shorepine/amychip/Arduino/pcm9211/wm8960.c

// wm89602.c

/******************************************************************************
  SparkFun WM8960 Arduino Library

  This library provides a set of functions to control (via I2C) the Wolfson 
  Microelectronics WM8960   Stereo CODEC with 1W Stereo Class D Speaker Drivers 
  and Headphone Drivers.

  Pete Lewis @ SparkFun Electronics
  October 14th, 2022
  https://github.com/sparkfun/SparkFun_WM8960_Arduino_Library
  
  This code was created using some code by Mike Grusin at SparkFun Electronics
  Included with the LilyPad MP3 example code found here:
  Revision history: version 1.0 2012/07/24 MDG Initial release
  https://github.com/sparkfun/LilyPad_MP3_Player

  Do you like this library? Help support SparkFun. Buy a board!

    SparkFun Audio Codec Breakout - WM8960 (QWIIC)
    https://www.sparkfun.com/products/21250
    
    All functions return 1 if the read/write was successful, and 0
    if there was a communications failure. You can ignore the return value
    if you just don't care anymore.

    For information on the data sent to and received from the CODEC,
    refer to the WM8960 datasheet at:
    https://github.com/sparkfun/SparkFun_Audio_Codec_Breakout_WM8960/blob/main/Documents/WM8960_datasheet_v4.2.pdf

  This code is released under the [MIT License](http://opensource.org/licenses/MIT).
  Please review the LICENSE.md file included with this example. If you have any questions 
  or concerns with licensing, please contact techsupport@sparkfun.com.
  Distributed as-is; no warranty is given.
******************************************************************************/

#include "wm8960.h"

// The WM8960 does not support I2C reads
// This means we must keep a local copy of all the register values
// We will instantiate with default values
// As we write to the device, we will also make sure
// To update our local copy as well, stored here in this array.
// Each register is 9-bits, so we will store them as a uint16_t
// They are in order from R0-R55, and we even keep blank spots for the
// "reserved" registers. This way we can use the register address macro 
// defines above to easiy access each local copy of each register.
// Example: _registerLocalCopy[WM8960_REG_LEFT_INPUT_VOLUME]
uint16_t _registerLocalCopy[56] = {
    0x0097, // R0 (0x00)
    0x0097, // R1 (0x01)
    0x0000, // R2 (0x02)
    0x0000, // R3 (0x03)
    0x0000, // R4 (0x04)
    0x0008, // F5 (0x05)
    0x0000, // R6 (0x06)
    0x000A, // R7 (0x07)
    0x01C0, // R8 (0x08)
    0x0000, // R9 (0x09)
    0x00FF, // R10 (0x0a)
    0x00FF, // R11 (0x0b)
    0x0000, // R12 (0x0C) RESERVED
    0x0000, // R13 (0x0D) RESERVED
    0x0000, // R14 (0x0E) RESERVED
    0x0000, // R15 (0x0F) RESERVED
    0x0000, // R16 (0x10)
    0x007B, // R17 (0x11)
    0x0100, // R18 (0x12)
    0x0032, // R19 (0x13)
    0x0000, // R20 (0x14)
    0x00C3, // R21 (0x15)
    0x00C3, // R22 (0x16)
    0x01C0, // R23 (0x17)
    0x0000, // R24 (0x18)
    0x0000, // R25 (0x19)
    0x0000, // R26 (0x1A)
    0x0000, // R27 (0x1B)
    0x0000, // R28 (0x1C)
    0x0000, // R29 (0x1D)
    0x0000, // R30 (0x1E) RESERVED
    0x0000, // R31 (0x1F) RESERVED
    0x0100, // R32 (0x20)
    0x0100, // R33 (0x21)
    0x0050, // R34 (0x22)
    0x0000, // R35 (0x23) RESERVED
    0x0000, // R36 (0x24) RESERVED
    0x0050, // R37 (0x25)
    0x0000, // R38 (0x26)
    0x0000, // R39 (0x27)
    0x0000, // R40 (0x28)
    0x0000, // R41 (0x29)
    0x0040, // R42 (0x2A)
    0x0000, // R43 (0x2B)
    0x0000, // R44 (0x2C)
    0x0050, // R45 (0x2D)
    0x0050, // R46 (0x2E)
    0x0000, // R47 (0x2F)
    0x0002, // R48 (0x30)
    0x0037, // R49 (0x31)
    0x0000, // R50 (0x32) RESERVED
    0x0080, // R51 (0x33)
    0x0008, // R52 (0x34)
    0x0031, // R53 (0x35)
    0x0026, // R54 (0x36)
    0x00e9, // R55 (0x37)
};

const uint16_t _registerDefaults[56] = {
    0x0097, // R0 (0x00)
    0x0097, // R1 (0x01)
    0x0000, // R2 (0x02)
    0x0000, // R3 (0x03)
    0x0000, // R4 (0x04)
    0x0008, // F5 (0x05)
    0x0000, // R6 (0x06)
    0x000A, // R7 (0x07)
    0x01C0, // R8 (0x08)
    0x0000, // R9 (0x09)
    0x00FF, // R10 (0x0a)
    0x00FF, // R11 (0x0b)
    0x0000, // R12 (0x0C) RESERVED
    0x0000, // R13 (0x0D) RESERVED
    0x0000, // R14 (0x0E) RESERVED
    0x0000, // R15 (0x0F) RESERVED
    0x0000, // R16 (0x10)
    0x007B, // R17 (0x11)
    0x0100, // R18 (0x12)
    0x0032, // R19 (0x13)
    0x0000, // R20 (0x14)
    0x00C3, // R21 (0x15)
    0x00C3, // R22 (0x16)
    0x01C0, // R23 (0x17)
    0x0000, // R24 (0x18)
    0x0000, // R25 (0x19)
    0x0000, // R26 (0x1A)
    0x0000, // R27 (0x1B)
    0x0000, // R28 (0x1C)
    0x0000, // R29 (0x1D)
    0x0000, // R30 (0x1E) RESERVED
    0x0000, // R31 (0x1F) RESERVED
    0x0100, // R32 (0x20)
    0x0100, // R33 (0x21)
    0x0050, // R34 (0x22)
    0x0000, // R35 (0x23) RESERVED
    0x0000, // R36 (0x24) RESERVED
    0x0050, // R37 (0x25)
    0x0000, // R38 (0x26)
    0x0000, // R39 (0x27)
    0x0000, // R40 (0x28)
    0x0000, // R41 (0x29)
    0x0040, // R42 (0x2A)
    0x0000, // R43 (0x2B)
    0x0000, // R44 (0x2C)
    0x0050, // R45 (0x2D)
    0x0050, // R46 (0x2E)
    0x0000, // R47 (0x2F)
    0x0002, // R48 (0x30)
    0x0037, // R49 (0x31)
    0x0000, // R50 (0x32) RESERVED
    0x0080, // R51 (0x33)
    0x0008, // R52 (0x34)
    0x0031, // R53 (0x35)
    0x0026, // R54 (0x36)
    0x00e9, // R55 (0x37)
};   


// This sets up with OUT3/HP at line level volume
// and with INPUT1 ADC coming in to i2s
void setup_wm8960_i2s() {

    enableVREF();
    enableVMID();

    enableLMIC();
    enableRMIC();

    connectLMN1();
    connectRMN1();

    disableLINMUTE();
    disableRINMUTE();
    
    setLINVOLDB(0);
    setRINVOLDB(0);
    
    setLMICBOOST(WM8960_MIC_BOOST_GAIN_0DB);
    setRMICBOOST(WM8960_MIC_BOOST_GAIN_0DB);

    connectLMIC2B();
    connectRMIC2B();

    enableAINL();
    enableAINR();
    
    disableLB2LO();
    disableRB2RO();

    enableLD2LO();
    enableRD2RO();
    setLB2LOVOL(WM8960_OUTPUT_MIXER_GAIN_NEG_21DB); 
    setRB2ROVOL(WM8960_OUTPUT_MIXER_GAIN_NEG_21DB); 

    enableLOMIX();
    enableROMIX();

    enablePLL();
    setPLLPRESCALE(WM8960_PLLPRESCALE_DIV_2);
    setSMD(WM8960_PLL_MODE_FRACTIONAL);
    setCLKSEL(WM8960_CLKSEL_PLL);
    setSYSCLKDIV(WM8960_SYSCLK_DIV_BY_2);
    setBCLKDIV(4);
    setDCLKDIV(WM8960_DCLKDIV_16);
    setPLLN(7);
    setPLLK(0x86, 0xC2, 0x26);
    setWL(WM8960_WL_16BIT);
    enablePeripheralMode();

    enableAdcLeft();
    enableAdcRight();

    enableDacLeft();
    enableDacRight();
    disableDacMute();

    disableLoopBack();

    disableDacMute();

    enableHeadphones();
    enableOUT3MIX();
    setHeadphoneVolumeDB(0.00); // line level 
}


extern void i2c_master_write_wm8960(uint8_t *data_wr, size_t size_wr);

// writeRegister(uint8_t reg, uint16_t value)
// General-purpose write to a register
// Returns 1 if successful, 0 if something failed (I2C error)
// The WM8960 has 9 bit registers.
// To write a register, we must do the following
// Send 3 bytes
// Byte0 = device address + read/write bit
// Control_byte_1 = register-to-write address (7-bits) plus 9th bit of data
// Control_byte_2 = remaining 8 bits of register data

void writeRegister(uint8_t reg, uint16_t value) {
  uint8_t data[2];

  // Shift reg over one spot to make room for the 9th bit of register data
  data[0] = (reg << 1); 
  
  // Shift value so only 9th bit is still there, plug it into 0th bit of 
  // control_byte_1
  data[0] |= (value >> 8); 

  data[1] = (uint8_t)(value & 0xFF);
  i2c_master_write_wm8960(data,2);  
}

// writeRegisterBit
// Writes a 0 or 1 to the desired bit in the desired register
void _writeRegisterBit(uint8_t registerAddress, uint8_t bitNumber, uint8_t bitValue)
{
    // Get the local copy of the register
    uint16_t regvalue = _registerLocalCopy[registerAddress]; 

    if(bitValue == 1) 
    {
      regvalue |= (1<<bitNumber); // Set only the bit we want  
    }
    else {
      regvalue &= ~(1<<bitNumber); // Clear only the bit we want  
    }

    // Write modified value to device
    // If successful, update local copy
    writeRegister(registerAddress, regvalue);
    _registerLocalCopy[registerAddress] = regvalue; 
}

// writeRegisterMultiBits
// This function writes data into the desired bits within the desired register
// Some settings require more than just flipping a single bit within a register.
// For these settings use this more advanced register write helper function.
// 
// For example, to change the LIN2BOOST setting to +6dB,
// I need to write a setting of 7 (aka +6dB) to the bits [3:1] in the 
// WM8960_REG_INPUT_BOOST_MIXER_1 register. Like so...
// _writeRegisterMultiBits(WM8960_REG_INPUT_BOOST_MIXER_1, 3, 1, 7);
void _writeRegisterMultiBits(uint8_t registerAddress, uint8_t settingMsbNum, uint8_t settingLsbNum, uint8_t setting)
{
  uint8_t numOfBits = (settingMsbNum - settingLsbNum) + 1;

  // Get the local copy of the register
  uint16_t regvalue = _registerLocalCopy[registerAddress]; 

  for(int i = 0 ; i < numOfBits ; i++)
  {
      regvalue &= ~(1 << (settingLsbNum + i)); // Clear bits we care about 
  }

  // Shift and set the bits from in incoming desired setting value
  regvalue |= (setting << settingLsbNum); 

  // Write modified value to device
  // If successful, update local copy
  writeRegister(registerAddress, regvalue);
  _registerLocalCopy[registerAddress] = regvalue; 
}

// enableVREF
// Necessary for all other functions of the CODEC
// VREF is a single bit we can flip in Register 25 (19h), WM8960_REG_PWR_MGMT_1
// VREF is bit 6, 0 = power down, 1 = power up
// Returns 1 if successful, 0 if something failed (I2C error)
void enableVREF()
{ 
  _writeRegisterBit(WM8960_REG_PWR_MGMT_1, 6, 1);
}

// disableVREF
// Use this to save power
// VREF is a single bit we can flip in Register 25 (19h), WM8960_REG_PWR_MGMT_1
// VREF is bit 6, 0 = power down, 1 = power up
// Returns 1 if successful, 0 if something failed (I2C error)
void disableVREF()
{
  _writeRegisterBit(WM8960_REG_PWR_MGMT_1, 6, 0);
}

// reset
// Use this to reset all registers to their default state
// Note, this can also be done by cycling power to the device
// Returns 1 if successful, 0 if something failed (I2C error)
void reset()
{
  // Doesn't matter which bit we flip, writing anything will cause the reset
  _writeRegisterBit(WM8960_REG_RESET, 7, 1);
  // Update our local copy of the registers to reflect the reset
  for(int i = 0 ; i < 56 ; i++)
  {
    _registerLocalCopy[i] = _registerDefaults[i]; 
  }
}

void enableAINL()
{ 
  _writeRegisterBit(WM8960_REG_PWR_MGMT_1, 5, 1);
}

void disableAINL()
{ 
  _writeRegisterBit(WM8960_REG_PWR_MGMT_1, 5, 0);
}

void enableAINR()
{
  _writeRegisterBit(WM8960_REG_PWR_MGMT_1, 4, 1);
}

void disableAINR()
{
  _writeRegisterBit(WM8960_REG_PWR_MGMT_1, 4, 0);
}

void enableLMIC()
{
  _writeRegisterBit(WM8960_REG_PWR_MGMT_3, 5, 1);
}

void disableLMIC()
{
  _writeRegisterBit(WM8960_REG_PWR_MGMT_3, 5, 0);
}

void enableRMIC()
{
  _writeRegisterBit(WM8960_REG_PWR_MGMT_3, 4, 1);
}

void disableRMIC()
{
  _writeRegisterBit(WM8960_REG_PWR_MGMT_3, 4, 0);
}

void enableLMICBOOST()
{
  _writeRegisterBit(WM8960_REG_PWR_MGMT_3, 5, 1);
}

void disableLMICBOOST()
{
  _writeRegisterBit(WM8960_REG_PWR_MGMT_3, 5, 0);
}

void enableRMICBOOST()
{
  _writeRegisterBit(WM8960_REG_PWR_MGMT_3, 4, 1);
}

void disableRMICBOOST()
{
  _writeRegisterBit(WM8960_REG_PWR_MGMT_3, 4, 0);
}

// PGA input signal select
// Each PGA (left and right) has a switch on its non-inverting input.
// On PGA_LEFT:
//  *You can select between VMID, LINPUT2 or LINPUT3
//  *Note, the inverting input of PGA_LEFT is perminantly connected to LINPUT1
// On PGA_RIGHT:
//  *You can select between VMIN, RINPUT2 or RINPUT3
//  *Note, the inverting input of PGA_RIGHT is perminantly connected to RINPUT1

// 3 options: WM8960_PGAL_LINPUT2, WM8960_PGAL_LINPUT3, WM8960_PGAL_VMID
void pgaLeftNonInvSignalSelect(uint8_t signal)
{
  // Clear LMP2 and LMP3
  // Necessary because the previous setting could have either set,
  // And we don't want to confuse the codec.
  // Only 1 input can be selected.

  // LMP3
  _writeRegisterBit(WM8960_REG_ADCL_SIGNAL_PATH, 7, 0); 

  // LMP2
  _writeRegisterBit(WM8960_REG_ADCL_SIGNAL_PATH, 6, 0); 
  
  if(signal == WM8960_PGAL_LINPUT2)
  {
    // LMP2
    _writeRegisterBit(WM8960_REG_ADCL_SIGNAL_PATH, 6, 1); 
  }
  else if(signal == WM8960_PGAL_LINPUT3)
  {
    // LMP3
    _writeRegisterBit(WM8960_REG_ADCL_SIGNAL_PATH, 7, 1); 
  }
  else if(signal == WM8960_PGAL_VMID)
  {
    // Don't set any bits. When both LMP2 and LMP3 are cleared, then the signal 
    // is set to VMID
  }
}

 // 3 options: WM8960_PGAR_RINPUT2, WM8960_PGAR_RINPUT3, WM8960_PGAR_VMID
void pgaRightNonInvSignalSelect(uint8_t signal)
{
  // Clear RMP2 and RMP3
  // Necessary because the previous setting could have either set,
  // And we don't want to confuse the codec.
  // Only 1 input can be selected.

  // RMP3
  _writeRegisterBit(WM8960_REG_ADCR_SIGNAL_PATH, 7, 0); 

  // RMP2
  _writeRegisterBit(WM8960_REG_ADCR_SIGNAL_PATH, 6, 0); 
  
  if(signal == WM8960_PGAR_RINPUT2)
  {
    // RMP2
    _writeRegisterBit(WM8960_REG_ADCR_SIGNAL_PATH, 6, 1); 
  }
  else if(signal == WM8960_PGAR_RINPUT3)
  {
    // RMP3
    _writeRegisterBit(WM8960_REG_ADCR_SIGNAL_PATH, 7, 1); 
  }
  else if(signal == WM8960_PGAR_VMID)
  {
    // Don't set any bits. When both RMP2 and RMP3 are cleared, then the signal 
    // is set to VMID
  }
}


// Connection from each INPUT1 to the inverting input of its PGA
void connectLMN1()
{
  _writeRegisterBit(WM8960_REG_ADCL_SIGNAL_PATH, 8, 1);
}

// Disconnect LINPUT1 to inverting input of Left Input PGA
void disconnectLMN1()
{
  _writeRegisterBit(WM8960_REG_ADCL_SIGNAL_PATH, 8, 0);
}

// Connect RINPUT1 from inverting input of Right Input PGA
void connectRMN1()
{
  _writeRegisterBit(WM8960_REG_ADCR_SIGNAL_PATH, 8, 1);
}

// Disconnect RINPUT1 to inverting input of Right Input PGA
void disconnectRMN1()
{
  _writeRegisterBit(WM8960_REG_ADCR_SIGNAL_PATH, 8, 0);
}

// Connections from output of PGAs to downstream "boost mixers".

// Connect Left Input PGA to Left Input Boost mixer
void connectLMIC2B()
{
  _writeRegisterBit(WM8960_REG_ADCL_SIGNAL_PATH, 3, 1);
}

// Disconnect Left Input PGA to Left Input Boost mixer
void disconnectLMIC2B()
{
  _writeRegisterBit(WM8960_REG_ADCL_SIGNAL_PATH, 3, 0);
}

// Connect Right Input PGA to Right Input Boost mixer
void connectRMIC2B()
{
  _writeRegisterBit(WM8960_REG_ADCR_SIGNAL_PATH, 3, 1);
}

// Disconnect Right Input PGA to Right Input Boost mixer
void disconnectRMIC2B()
{
  _writeRegisterBit(WM8960_REG_ADCR_SIGNAL_PATH, 3, 0);
}

// 0-63, (0 = -17.25dB) <<-- 0.75dB steps -->> (63 = +30dB)
void setLINVOL(uint8_t volume) 
{
  if(volume > 63) volume = 63; // Limit incoming values max
  _writeRegisterMultiBits(WM8960_REG_LEFT_INPUT_VOLUME,5,0,volume);
  pgaLeftIPVUSet();
}

// setLINVOLDB
// Sets the volume of the PGA input buffer amp to a specified dB value 
// passed in as a float argument.
// Valid dB settings are -17.25 up to +30.00
// -17.25 = -17.25dB (MIN)
// ... 0.75dB steps ...
// 30.00 = +30.00dB  (MAX)
void setLINVOLDB(float dB)
{
  // Create an unsigned integer volume setting variable we can send to 
  // setLINVOL()
  uint8_t volume = convertDBtoSetting(dB, WM8960_PGA_GAIN_OFFSET, WM8960_PGA_GAIN_STEPSIZE, WM8960_PGA_GAIN_MIN, WM8960_PGA_GAIN_MAX);

  setLINVOL(volume);
}

// 0-63, (0 = -17.25dB) <<-- 0.75dB steps -->> (63 = +30dB)
void setRINVOL(uint8_t volume) 
{
  if(volume > 63) volume = 63; // Limit incoming values max
  _writeRegisterMultiBits(WM8960_REG_RIGHT_INPUT_VOLUME,5,0,volume);
  pgaRightIPVUSet();
}

// setRINVOLDB
// Sets the volume of the PGA input buffer amp to a specified dB value 
// passed in as a float argument.
// Valid dB settings are -17.25 up to +30.00
// -17.25 = -17.25dB (MIN)
// ... 0.75dB steps ...
// 30.00 = +30.00dB  (MAX)
void setRINVOLDB(float dB)
{
  // Create an unsigned integer volume setting variable we can send to 
  // setRINVOL()
  uint8_t volume = convertDBtoSetting(dB, WM8960_PGA_GAIN_OFFSET, WM8960_PGA_GAIN_STEPSIZE, WM8960_PGA_GAIN_MIN, WM8960_PGA_GAIN_MAX);
  setRINVOL(volume);
}

// Zero Cross prevents zipper sounds on volume changes
// Sets both left and right PGAs
void enablePgaZeroCross()
{
  _writeRegisterBit(WM8960_REG_LEFT_INPUT_VOLUME, 6, 1);
  _writeRegisterBit(WM8960_REG_RIGHT_INPUT_VOLUME, 6, 1);
}

void disablePgaZeroCross()
{
  _writeRegisterBit(WM8960_REG_LEFT_INPUT_VOLUME, 6, 0);
  _writeRegisterBit(WM8960_REG_RIGHT_INPUT_VOLUME, 6, 0);
}

void enableLINMUTE()
{
  _writeRegisterBit(WM8960_REG_LEFT_INPUT_VOLUME, 7, 1);
}

void disableLINMUTE()
{
  _writeRegisterBit(WM8960_REG_LEFT_INPUT_VOLUME, 7, 0);
  _writeRegisterBit(WM8960_REG_LEFT_INPUT_VOLUME, 8, 1);
}

void enableRINMUTE()
{
  _writeRegisterBit(WM8960_REG_RIGHT_INPUT_VOLUME, 7, 1);
}

void disableRINMUTE()
{
  _writeRegisterBit(WM8960_REG_RIGHT_INPUT_VOLUME, 7, 0);
  _writeRegisterBit(WM8960_REG_RIGHT_INPUT_VOLUME, 8, 1);
}

// Causes left and right input PGA volumes to be updated (LINVOL and RINVOL)
void pgaLeftIPVUSet()
{
  _writeRegisterBit(WM8960_REG_LEFT_INPUT_VOLUME, 8, 1);
}

 // Causes left and right input PGA volumes to be updated (LINVOL and RINVOL)
void pgaRightIPVUSet()
{
  _writeRegisterBit(WM8960_REG_RIGHT_INPUT_VOLUME, 8, 1);
}


// Input Boosts

// 0-3, 0 = +0dB, 1 = +13dB, 2 = +20dB, 3 = +29dB
void setLMICBOOST(uint8_t boost_gain) 
{
  if(boost_gain > 3) boost_gain = 3; // Limit incoming values max
  _writeRegisterMultiBits(WM8960_REG_ADCL_SIGNAL_PATH,5,4,boost_gain);
}

// 0-3, 0 = +0dB, 1 = +13dB, 2 = +20dB, 3 = +29dB
void setRMICBOOST(uint8_t boost_gain) 
{
  if(boost_gain > 3) boost_gain = 3; // Limit incoming values max
  _writeRegisterMultiBits(WM8960_REG_ADCR_SIGNAL_PATH,5,4,boost_gain);
}

// 0-7, 0 = Mute, 1 = -12dB ... 3dB steps ... 7 = +6dB
void setLIN3BOOST(uint8_t boost_gain) 
{
  if(boost_gain > 7) boost_gain = 7; // Limit incoming values max
  _writeRegisterMultiBits(WM8960_REG_INPUT_BOOST_MIXER_1,6,4,boost_gain);
}

// 0-7, 0 = Mute, 1 = -12dB ... 3dB steps ... 7 = +6dB
void setLIN2BOOST(uint8_t boost_gain) 
{
  if(boost_gain > 7) boost_gain = 7; // Limit incoming values max
  _writeRegisterMultiBits(WM8960_REG_INPUT_BOOST_MIXER_1,3,1,boost_gain);
}

// 0-7, 0 = Mute, 1 = -12dB ... 3dB steps ... 7 = +6dB
void setRIN3BOOST(uint8_t boost_gain) 
{
  if(boost_gain > 7) boost_gain = 7; // Limit incoming values max
  _writeRegisterMultiBits(WM8960_REG_INPUT_BOOST_MIXER_2,6,4,boost_gain);
}

// 0-7, 0 = Mute, 1 = -12dB ... 3dB steps ... 7 = +6dB  
void setRIN2BOOST(uint8_t boost_gain) 
{
  if(boost_gain > 7) boost_gain = 7; // Limit incoming values max
  _writeRegisterMultiBits(WM8960_REG_INPUT_BOOST_MIXER_2,3,1,boost_gain);
}

// Mic Bias control
void enableMicBias()
{
  _writeRegisterBit(WM8960_REG_PWR_MGMT_1, 1, 1);
}

void disableMicBias()
{
  _writeRegisterBit(WM8960_REG_PWR_MGMT_1, 1, 0);
}

// WM8960_MIC_BIAS_VOLTAGE_0_9_AVDD (0.9*AVDD) 
// or WM8960_MIC_BIAS_VOLTAGE_0_65_AVDD (0.65*AVDD)
void setMicBiasVoltage(uint8_t voltage)
{
  _writeRegisterBit(WM8960_REG_ADDITIONAL_CONTROL_4, 0, voltage);
}

/////////////////////////////////////////////////////////
///////////////////////////////////////////////////////// ADC
/////////////////////////////////////////////////////////

void enableAdcLeft()
{
  _writeRegisterBit(WM8960_REG_PWR_MGMT_1, 3, 1);
}

void disableAdcLeft()
{
  _writeRegisterBit(WM8960_REG_PWR_MGMT_1, 3, 0);
}

void enableAdcRight()
{
  _writeRegisterBit(WM8960_REG_PWR_MGMT_1, 2, 1);
}

void disableAdcRight()
{
  _writeRegisterBit(WM8960_REG_PWR_MGMT_1, 2, 0);
}

// ADC digital volume
// Note, also needs to handle control of the ADCVU bits (volume update).
// Valid inputs are 0-255
// 0 = mute
// 1 = -97dB
// ... 0.5dB steps up to
// 195 = +0dB
// 255 = +30dB

void setAdcLeftDigitalVolume(uint8_t volume)
{
  _writeRegisterMultiBits(WM8960_REG_LEFT_ADC_VOLUME,7,0,volume);
  adcLeftADCVUSet();
}
void setAdcRightDigitalVolume(uint8_t volume)
{
  _writeRegisterMultiBits(WM8960_REG_RIGHT_ADC_VOLUME,7,0,volume);
  adcRightADCVUSet();
}

// Causes left and right input adc digital volumes to be updated
void adcLeftADCVUSet()
{
  _writeRegisterBit(WM8960_REG_LEFT_ADC_VOLUME, 8, 1);
}

// Causes left and right input adc digital volumes to be updated
void adcRightADCVUSet()
{
  _writeRegisterBit(WM8960_REG_RIGHT_ADC_VOLUME, 8, 1);
}

// ADC digital volume DB
// Sets the volume of the ADC to a specified dB value passed in as a float 
// argument.
// Valid dB settings are -97.00 up to +30.0 (0.5dB steps)
// -97.50 (or lower) = MUTE
// -97.00 = -97.00dB (MIN)
// ... 0.5dB steps ...
// 30.00 = +30.00dB  (MAX)

void setAdcLeftDigitalVolumeDB(float dB)
{
  // Create an unsigned integer volume setting variable we can send to 
  // setAdcLeftDigitalVolume()
  uint8_t volume = convertDBtoSetting(dB, WM8960_ADC_GAIN_OFFSET, WM8960_ADC_GAIN_STEPSIZE, WM8960_ADC_GAIN_MIN, WM8960_ADC_GAIN_MAX);
  setAdcLeftDigitalVolume(volume);
}
void setAdcRightDigitalVolumeDB(float dB)
{
  // Create an unsigned integer volume setting variable we can send to 
  // setAdcRightDigitalVolume()
  uint8_t volume = convertDBtoSetting(dB, WM8960_ADC_GAIN_OFFSET, WM8960_ADC_GAIN_STEPSIZE, WM8960_ADC_GAIN_MIN, WM8960_ADC_GAIN_MAX);

  setAdcRightDigitalVolume(volume);
}

/////////////////////////////////////////////////////////
///////////////////////////////////////////////////////// ALC
/////////////////////////////////////////////////////////

// Automatic Level Control
// Note that when the ALC function is enabled, the settings of registers 0 and 
// 1 (LINVOL, IPVU, LIZC, LINMUTE, RINVOL, RIZC and RINMUTE) are ignored.
void enableAlc(uint8_t mode)
{
  uint8_t bit8 = (mode>>1);
  uint8_t bit7 = (mode & 0b00000001);
  _writeRegisterBit(WM8960_REG_ALC1, 8, bit8);
  _writeRegisterBit(WM8960_REG_ALC1, 7, bit7);
}

 // Also sets alc sample rate to match global sample rate.
void disableAlc()
{
  _writeRegisterBit(WM8960_REG_ALC1, 8, 0);
  _writeRegisterBit(WM8960_REG_ALC1, 7, 0);
}

// Valid inputs are 0-15, 0 = -22.5dB FS, ... 1.5dB steps ... , 15 = -1.5dB FS
void setAlcTarget(uint8_t target) 
{
  if(target > 15) target = 15; // Limit incoming values max
  _writeRegisterMultiBits(WM8960_REG_ALC1,3,0,target);
}

// Valid inputs are 0-10, 0 = 24ms, 1 = 48ms, ... 10 = 24.58seconds
void setAlcDecay(uint8_t decay) 
{
  if(decay > 10) decay = 10; // Limit incoming values max
  _writeRegisterMultiBits(WM8960_REG_ALC3,7,4,decay);
}

// Valid inputs are 0-10, 0 = 6ms, 1 = 12ms, 2 = 24ms, ... 10 = 6.14seconds
void setAlcAttack(uint8_t attack) 
{
  if(attack > 10) attack = 10; // Limit incoming values max
  _writeRegisterMultiBits(WM8960_REG_ALC3,3,0,attack);
}

// Valid inputs are 0-7, 0 = -12dB, ... 7 = +30dB
void setAlcMaxGain(uint8_t maxGain) 
{
  if(maxGain > 7) maxGain = 7; // Limit incoming values max
  _writeRegisterMultiBits(WM8960_REG_ALC1,6,4,maxGain);
}

// Valid inputs are 0-7, 0 = -17.25dB, ... 7 = +24.75dB
void setAlcMinGain(uint8_t minGain) 
{
  if(minGain > 7) minGain = 7; // Limit incoming values max
  _writeRegisterMultiBits(WM8960_REG_ALC2,6,4,minGain);
}

// Valid inputs are 0-15, 0 = 0ms, ... 15 = 43.691s
void setAlcHold(uint8_t hold) 
{
  if(hold > 15) hold = 15; // Limit incoming values max
  _writeRegisterMultiBits(WM8960_REG_ALC2,3,0,hold);
}

// Peak Limiter
void enablePeakLimiter()
{
  _writeRegisterBit(WM8960_REG_ALC3, 8, 1);
}

void disablePeakLimiter()
{
  _writeRegisterBit(WM8960_REG_ALC3, 8, 0);
}

// Noise Gate
void enableNoiseGate()
{
  _writeRegisterBit(WM8960_REG_NOISE_GATE, 0, 1);
}

void disableNoiseGate()
{
  _writeRegisterBit(WM8960_REG_NOISE_GATE, 0, 0);
}

// 0-31, 0 = -76.5dBfs, 31 = -30dBfs
void setNoiseGateThreshold(uint8_t threshold) 
{
  
}

/////////////////////////////////////////////////////////
///////////////////////////////////////////////////////// DAC
/////////////////////////////////////////////////////////

// Enable/disble each channel
void enableDacLeft()
{
  _writeRegisterBit(WM8960_REG_PWR_MGMT_2, 8, 1);
}

void disableDacLeft()
{
  _writeRegisterBit(WM8960_REG_PWR_MGMT_2, 8, 0);
}

void enableDacRight()
{
  _writeRegisterBit(WM8960_REG_PWR_MGMT_2, 7, 1);
}

void disableDacRight()
{
  _writeRegisterBit(WM8960_REG_PWR_MGMT_2, 7, 0);
}

// DAC digital volume
// Valid inputs are 0-255
// 0 = mute
// 1 = -127dB
// ... 0.5dB steps up to
// 255 = 0dB
void setDacLeftDigitalVolume(uint8_t volume)
{
  _writeRegisterMultiBits(WM8960_REG_LEFT_DAC_VOLUME,7,0,volume);
  dacLeftDACVUSet();
}

void setDacRightDigitalVolume(uint8_t volume)
{
  _writeRegisterMultiBits(WM8960_REG_RIGHT_DAC_VOLUME,7,0,volume);
  dacRightDACVUSet();
}

// Causes left and right input dac digital volumes to be updated
void dacLeftDACVUSet()
{
  _writeRegisterBit(WM8960_REG_LEFT_DAC_VOLUME, 8, 1);
}

 // Causes left and right input dac digital volumes to be updated
void dacRightDACVUSet()
{
  _writeRegisterBit(WM8960_REG_RIGHT_DAC_VOLUME, 8, 1);
}   

// DAC digital volume DB
// Sets the volume of the DAC to a specified dB value passed in as a float 
// argument.
// Valid dB settings are -97.00 up to +30.0 (0.5dB steps)
// -97.50 (or lower) = MUTE
// -97.00 = -97.00dB (MIN)
// ... 0.5dB steps ...
// 30.00 = +30.00dB  (MAX)

void setDacLeftDigitalVolumeDB(float dB)
{
  // Create an unsigned integer volume setting variable we can send to 
  // setDacLeftDigitalVolume()
  uint8_t volume = convertDBtoSetting(dB, WM8960_DAC_GAIN_OFFSET, WM8960_DAC_GAIN_STEPSIZE, WM8960_DAC_GAIN_MIN, WM8960_DAC_GAIN_MAX);
  setDacLeftDigitalVolume(volume);
}

void setDacRightDigitalVolumeDB(float dB)
{
  // Create an unsigned integer volume setting variable we can send to 
  // setDacRightDigitalVolume()
  uint8_t volume = convertDBtoSetting(dB, WM8960_DAC_GAIN_OFFSET, WM8960_DAC_GAIN_STEPSIZE, WM8960_DAC_GAIN_MIN, WM8960_DAC_GAIN_MAX);
  setDacRightDigitalVolume(volume);
}

// DAC mute
void enableDacMute()
{
  _writeRegisterBit(WM8960_REG_ADC_DAC_CTRL_1, 3, 1);
}

void disableDacMute()
{
  _writeRegisterBit(WM8960_REG_ADC_DAC_CTRL_1, 3, 0);
}

// 3D Stereo Enhancement
// 3D enable/disable
void enable3d()
{
  _writeRegisterBit(WM8960_REG_3D_CONTROL, 0, 1);
}

void disable3d()
{
  _writeRegisterBit(WM8960_REG_3D_CONTROL, 0, 0);
}

void set3dDepth(uint8_t depth) // 0 = 0%, 15 = 100%
{
  if(depth > 15) depth = 15; // Limit incoming values max
  _writeRegisterMultiBits(WM8960_REG_3D_CONTROL,4,1,depth);
}

// DAC output -6dB attentuation enable/disable
void enableDac6dbAttenuation()
{
  _writeRegisterBit(WM8960_REG_ADC_DAC_CTRL_1, 7, 1);
}

void disableDac6dbAttentuation()
{
  _writeRegisterBit(WM8960_REG_ADC_DAC_CTRL_1, 7, 0);
}

/////////////////////////////////////////////////////////
///////////////////////////////////////////////////////// OUTPUT mixers
/////////////////////////////////////////////////////////

// What's connected to what? Oh so many options...
// LOMIX    Left Output Mixer
// ROMIX    Right Output Mixer
// OUT3MIX      Mono Output Mixer

// Enable/disable left and right output mixers
void enableLOMIX()
{
  _writeRegisterBit(WM8960_REG_PWR_MGMT_3, 3, 1);
}

void disableLOMIX()
{
  _writeRegisterBit(WM8960_REG_PWR_MGMT_3, 3, 0);
}

void enableROMIX()
{
  _writeRegisterBit(WM8960_REG_PWR_MGMT_3, 2, 1);
}

void disableROMIX()
{
  _writeRegisterBit(WM8960_REG_PWR_MGMT_3, 2, 0);
}

void enableOUT3MIX()
{
  _writeRegisterBit(WM8960_REG_PWR_MGMT_2, 1, 1);
}

void disableOUT3MIX()
{
  _writeRegisterBit(WM8960_REG_PWR_MGMT_2, 1, 0);
}

// Enable/disable audio path connections/vols to/from output mixers
// See datasheet page 35 for a nice image of all the connections.
void enableLI2LO()
{
  _writeRegisterBit(WM8960_REG_LEFT_OUT_MIX_1, 7, 1);
}

void disableLI2LO()
{
  _writeRegisterBit(WM8960_REG_LEFT_OUT_MIX_1, 7, 0);
}

// Valid inputs are 0-7. 0 = 0dB ...3dB steps... 7 = -21dB
void setLI2LOVOL(uint8_t volume) 
{
  if(volume > 7) volume = 7; // Limit incoming values max
  _writeRegisterMultiBits(WM8960_REG_LEFT_OUT_MIX_1,6,4,volume);
}

void enableLB2LO()
{
  _writeRegisterBit(WM8960_REG_BYPASS_1, 7, 1);
}

void disableLB2LO()
{
  _writeRegisterBit(WM8960_REG_BYPASS_1, 7, 0);
}

// Valid inputs are 0-7. 0 = 0dB ...3dB steps... 7 = -21dB
void setLB2LOVOL(uint8_t volume) 
{
  if(volume > 7) volume = 7; // Limit incoming values max
  _writeRegisterMultiBits(WM8960_REG_BYPASS_1,6,4,volume);
}

void enableLD2LO()
{
  _writeRegisterBit(WM8960_REG_LEFT_OUT_MIX_1, 8, 1);
}

void disableLD2LO()
{
  _writeRegisterBit(WM8960_REG_LEFT_OUT_MIX_1, 8, 0);
}

void enableRI2RO()
{
  _writeRegisterBit(WM8960_REG_RIGHT_OUT_MIX_2, 7, 1);
}

void disableRI2RO()
{
  _writeRegisterBit(WM8960_REG_RIGHT_OUT_MIX_2, 7, 0);
}

// Valid inputs are 0-7. 0 = 0dB ...3dB steps... 7 = -21dB
void setRI2ROVOL(uint8_t volume) 
{
  if(volume > 7) volume = 7; // Limit incoming values max
  _writeRegisterMultiBits(WM8960_REG_RIGHT_OUT_MIX_2,6,4,volume);
}

void enableRB2RO()
{
  _writeRegisterBit(WM8960_REG_BYPASS_2, 7, 1);
}

void disableRB2RO()
{
  _writeRegisterBit(WM8960_REG_BYPASS_2, 7, 0);
}

// Valid inputs are 0-7. 0 = 0dB ...3dB steps... 7 = -21dB
void setRB2ROVOL(uint8_t volume) 
{
  if(volume > 7) volume = 7; // Limit incoming values max
  _writeRegisterMultiBits(WM8960_REG_BYPASS_2,6,4,volume);
}

void enableRD2RO()
{
  _writeRegisterBit(WM8960_REG_RIGHT_OUT_MIX_2, 8, 1);
}

void disableRD2RO()
{
  _writeRegisterBit(WM8960_REG_RIGHT_OUT_MIX_2, 8, 0);
}

// Mono Output mixer. 
// Note, for capless HPs, we'll want this to output a buffered VMID.
// To do this, we need to disable both of these connections.
void enableLI2MO()
{
  _writeRegisterBit(WM8960_REG_MONO_OUT_MIX_1, 7, 1);
}

void disableLI2MO()
{
  _writeRegisterBit(WM8960_REG_MONO_OUT_MIX_1, 7, 0);
}

void enableRI2MO()
{
  _writeRegisterBit(WM8960_REG_MONO_OUT_MIX_2, 7, 1);
}

void disableRI2MO()
{
  _writeRegisterBit(WM8960_REG_MONO_OUT_MIX_2, 7, 0);
}

// Enables VMID in the WM8960_REG_PWR_MGMT_2 register, and set's it to 
// playback/record settings of 2*50Kohm.
// Note, this function is only hear for backwards compatibility with the
// original releases of this library. It is recommended to use the
// setVMID() function instead.
void enableVMID()
{
  setVMID(WM8960_VMIDSEL_2X50KOHM);
}

void disableVMID()
{
  setVMID(WM8960_VMIDSEL_DISABLED);
}

// setVMID
// Sets the VMID signal to one of three possible settings.
// 4 options:
// WM8960_VMIDSEL_DISABLED
// WM8960_VMIDSEL_2X50KOHM (playback / record)
// WM8960_VMIDSEL_2X250KOHM (for low power / standby)
// WM8960_VMIDSEL_2X5KOHM (for fast start-up)
void setVMID(uint8_t setting)
{
  _writeRegisterMultiBits(WM8960_REG_PWR_MGMT_1, 8, 7, setting);
}

/////////////////////////////////////////////////////////
///////////////////////////////////////////////////////// Headphones
/////////////////////////////////////////////////////////

// Enable and disable headphones (mute)
void enableHeadphones()
{
  enableRightHeadphone();
  enableLeftHeadphone();
}

void disableHeadphones()
{
  disableRightHeadphone();
  disableLeftHeadphone();
}

void enableRightHeadphone()
{
  _writeRegisterBit(WM8960_REG_PWR_MGMT_2, 5, 1);
}

void disableRightHeadphone()
{
  _writeRegisterBit(WM8960_REG_PWR_MGMT_2, 5, 0);
}

void enableLeftHeadphone()
{
  _writeRegisterBit(WM8960_REG_PWR_MGMT_2, 6, 1);
}

void disableLeftHeadphone()
{
  _writeRegisterBit(WM8960_REG_PWR_MGMT_2, 6, 0);
}

void enableHeadphoneStandby()
{
  _writeRegisterBit(WM8960_REG_ANTI_POP_1, 0, 1);
}

void disableHeadphoneStandby()
{
  _writeRegisterBit(WM8960_REG_ANTI_POP_1, 0, 0);
}

// SetHeadphoneVolume
// Sets the volume for both left and right headphone outputs
// 
// Although you can control each headphone output independently, here we are
// Going to assume you want both left and right to do the same thing.
// 
// Valid inputs: 47-127. 0-47 = mute, 48 = -73dB ... 1dB steps ... 127 = +6dB
void setHeadphoneVolume(uint8_t volume) 
{       
  // Updates both left and right channels
    // Handles the OUT1VU (volume update) bit control, so that it happens at the 
  // same time on both channels. Note, we must also make sure that the outputs 
  // are enabled in the WM8960_REG_PWR_MGMT_2 [6:5]
  // Grab local copy of register
  // Modify the bits we need to
  // Write register in device, including the volume update bit write
  // If successful, save locally.

  // Limit inputs
  if (volume > 127) volume = 127;

  // LEFT
    _writeRegisterMultiBits(WM8960_REG_LOUT1_VOLUME,6,0,volume);
  // RIGHT
    _writeRegisterMultiBits(WM8960_REG_ROUT1_VOLUME,6,0,volume);
  // UPDATES

  // Updated left channel
    _writeRegisterBit(WM8960_REG_LOUT1_VOLUME, 8, 1); 

  // Updated right channel
    _writeRegisterBit(WM8960_REG_ROUT1_VOLUME, 8, 1); 
}

// Set headphone volume dB
// Sets the volume of the headphone output buffer amp to a specified dB value 
// passed in as a float argument.
// Valid dB settings are -74.0 up to +6.0
// Note, we are accepting float arguments here, in order to keep it consistent
// with other volume setting functions in this library that can do partial dB
// values (such as the PGA, ADC and DAC gains).
// -74 (or lower) = MUTE
// -73 = -73dB (MIN)
// ... 1dB steps ...
// 0 = 0dB
// ... 1dB steps ...
// 6 = +6dB  (MAX)
void setHeadphoneVolumeDB(float dB)
{
  // Create an unsigned integer volume setting variable we can send to 
  // setHeadphoneVolume()
  uint8_t volume = convertDBtoSetting(dB, WM8960_HP_GAIN_OFFSET, WM8960_HP_GAIN_STEPSIZE, WM8960_HP_GAIN_MIN, WM8960_HP_GAIN_MAX);

  setHeadphoneVolume(volume);
}

// Zero Cross prevents zipper sounds on volume changes
// Sets both left and right Headphone outputs
void enableHeadphoneZeroCross()
{
  // Left
  _writeRegisterBit(WM8960_REG_LOUT1_VOLUME, 7, 1); 

  // Right
  _writeRegisterBit(WM8960_REG_ROUT1_VOLUME, 7, 1); 
}

void disableHeadphoneZeroCross()
{
  // Left
  _writeRegisterBit(WM8960_REG_LOUT1_VOLUME, 7, 0); 

  // Right
  _writeRegisterBit(WM8960_REG_ROUT1_VOLUME, 7, 0); 
}

/////////////////////////////////////////////////////////
///////////////////////////////////////////////////////// Speakers
/////////////////////////////////////////////////////////

// Enable and disable speakers (mute)
void enableSpeakers()
{
  enableRightSpeaker();
  enableLeftSpeaker();
}

void disableSpeakers()
{
  disableRightSpeaker();
  disableLeftSpeaker();
}

void enableRightSpeaker()
{
  // SPK_OP_EN
  _writeRegisterBit(WM8960_REG_CLASS_D_CONTROL_1, 7, 1); 

  // SPKR
  _writeRegisterBit(WM8960_REG_PWR_MGMT_2, 3, 1); 
}

void disableRightSpeaker()
{
  // SPK_OP_EN
  _writeRegisterBit(WM8960_REG_CLASS_D_CONTROL_1, 7, 0); 

  // SPKR
  _writeRegisterBit(WM8960_REG_PWR_MGMT_2, 3, 0); 
}

void enableLeftSpeaker()
{
  // SPK_OP_EN
  _writeRegisterBit(WM8960_REG_CLASS_D_CONTROL_1, 6, 1); 

  // SPKL
  _writeRegisterBit(WM8960_REG_PWR_MGMT_2, 4, 1); 
}

void disableLeftSpeaker()
{
  // SPK_OP_EN
  _writeRegisterBit(WM8960_REG_CLASS_D_CONTROL_1, 6, 0); 

  // SPKL
  _writeRegisterBit(WM8960_REG_PWR_MGMT_2, 4, 0); 
}

// SetSpeakerVolume
// Sets to volume for both left and right speaker outputs
// 
// Although you can control each Speaker output independently, here we are
// Going to assume you want both left and right to do the same thing.
// 
// Valid inputs are 47-127. 0-47 = mute, 48 = -73dB, ... 1dB steps ... , 127 = +6dB
void setSpeakerVolume(uint8_t volume) 
{       
  // Updates both left and right channels
    // Handles the SPKVU (volume update) bit control, so that it happens at the 
  // same time on both channels. Note, we must also make sure that the outputs 
  // are enabled in the WM8960_REG_PWR_MGMT_2 [4:3], and the class D control 
  // reg WM8960_REG_CLASS_D_CONTROL_1 [7:6]

  // Limit inputs
  if (volume > 127) volume = 127;

  // LEFT
  _writeRegisterMultiBits(WM8960_REG_LOUT2_VOLUME,6,0,volume);

  // RIGHT
  _writeRegisterMultiBits(WM8960_REG_ROUT2_VOLUME,6,0,volume);

  // SPKVU

  // Updated left channel
  _writeRegisterBit(WM8960_REG_LOUT2_VOLUME, 8, 1); 

  // Updated right channel
  _writeRegisterBit(WM8960_REG_ROUT2_VOLUME, 8, 1); 

}

// Set speaker volume dB
// Sets the volume of the class-d speaker output amp to a specified dB value 
// passed in as a float argument.
// Valid dB settings are -74.0 up to +6.0
// Note, we are accepting float arguments here, in order to keep it consistent
// with other volume setting functions in this library that can do partial dB
// values (such as the PGA, ADC and DAC gains).
// -74 (or lower) = MUTE
// -73 = -73dB (MIN)
// ... 1dB steps ...
// 0 = 0dB
// ... 1dB steps ...
// 6 = +6dB  (MAX)
void setSpeakerVolumeDB(float dB)
{
  // Create an unsigned integer volume setting variable we can send to 
  // setSpeakerVolume()
  uint8_t volume = convertDBtoSetting(dB, WM8960_SPEAKER_GAIN_OFFSET, WM8960_SPEAKER_GAIN_STEPSIZE, WM8960_SPEAKER_GAIN_MIN, WM8960_SPEAKER_GAIN_MAX);
  setSpeakerVolume(volume);
}

// Zero Cross prevents zipper sounds on volume changes
// Sets both left and right Speaker outputs
void enableSpeakerZeroCross()
{
  // Left
  _writeRegisterBit(WM8960_REG_LOUT2_VOLUME, 7, 1); 

  // Right
  _writeRegisterBit(WM8960_REG_ROUT2_VOLUME, 7, 1); 
}

void disableSpeakerZeroCross()
{
  // Left
  _writeRegisterBit(WM8960_REG_LOUT2_VOLUME, 7, 0); 

  // Right
  _writeRegisterBit(WM8960_REG_ROUT2_VOLUME, 7, 0); 
}

// SetSpeakerDcGain
// DC and AC gain - allows signal to be higher than the DACs swing
// (use only if your SPKVDD is high enough to handle a larger signal)
// Valid inputs are 0-5
// 0 = +0dB (1.0x boost) ... up to ... 5 = +5.1dB (1.8x boost)
void setSpeakerDcGain(uint8_t gain)
{
  if(gain > 5) gain = 5; // Limit incoming values max
  _writeRegisterMultiBits(WM8960_REG_CLASS_D_CONTROL_3,5,3,gain);
}

// SetSpeakerAcGain
// DC and AC gain - allows signal to be higher than the DACs swing
// (use only if your SPKVDD is high enough to handle a larger signal)
// Valid inputs are 0-5
// 0 = +0dB (1.0x boost) ... up to ... 5 = +5.1dB (1.8x boost)
void setSpeakerAcGain(uint8_t gain)
{
  if(gain > 5) gain = 5; // Limit incoming values max
  _writeRegisterMultiBits(WM8960_REG_CLASS_D_CONTROL_3,2,0,gain);
}

//////////////////////////////////////////////
////////////////////////////////////////////// Digital audio interface control
//////////////////////////////////////////////

// Defaults to I2S, peripheral-mode, 24-bit word length

// Loopback
// When enabled, the output data from the ADC audio interface is fed directly 
// into the DAC data input.
void enableLoopBack()
{
  _writeRegisterBit(WM8960_REG_AUDIO_INTERFACE_2, 0, 1);
}

void disableLoopBack()
{
  _writeRegisterBit(WM8960_REG_AUDIO_INTERFACE_2, 0, 0);
}

/////////////////////////////////////////////////////////
///////////////////////////////////////////////////////// Clock controls
/////////////////////////////////////////////////////////

// Getting the Frequency of SampleRate as we wish
// Our MCLK (an external clock on the SFE breakout board) is 24.0MHz.
// According to table 40 (DS pg 58), we want SYSCLK to be 11.2896 for a SR of 
// 44.1KHz. To get that Desired Output (SYSCLK), we need the following settings 
// on the PLL stuff, as found on table 45 (ds pg 61):
// PRESCALE DIVIDE (PLLPRESCALE): 2
// POSTSCALE DVIDE (SYSCLKDIV[1:0]): 2
// FIXED POST-DIVIDE: 4
// R: 7.5264 
// N: 7h
// K: 86C226h

// Example at bottom of table 46, shows that we should be in fractional mode 
// for a 44.1KHz.

// In terms of registers, this is what we want for 44.1KHz
// PLLEN=1          (PLL enable)
// PLLPRESCALE=1    (divide by 2) *This get's us from MCLK (24MHz) down to 12MHZ 
// for F2.
// PLLN=7h          (PLL N value) *this is "int R"
// PLLK=86C226h     (PLL K value) *this is int ( 2^24 * (R- intR)) 
// SDM=1            (Fractional mode)
// CLKSEL=1         (PLL select) 
// MS=0             (Peripheral mode)
// WL=00            (16 bits)
// SYSCLKDIV=2      (Divide by 2)
// ADCDIV=000       (Divide by 1) = 44.1kHz
// DACDIV=000       (Divide by 1) = 44.1kHz
// BCLKDIV=0100     (Divide by 4) = 64fs
// DCLKDIV=111      (Divide by 16) = 705.6kHz

// And now for the functions that will set these registers...
void enablePLL()
{
  _writeRegisterBit(WM8960_REG_PWR_MGMT_2, 0, 1);
}

void disablePLL()
{
  _writeRegisterBit(WM8960_REG_PWR_MGMT_2, 0, 0);
}

void setPLLPRESCALE(uint8_t div)
{
  _writeRegisterBit(WM8960_REG_PLL_N, 4, div);
}

void setPLLN(uint8_t n)
{
  _writeRegisterMultiBits(WM8960_REG_PLL_N,3,0,n); 
}

// Send each nibble of 24-bit value for value K
void setPLLK(uint8_t one, uint8_t two, uint8_t three) 
{
  _writeRegisterMultiBits(WM8960_REG_PLL_K_1,5,0,one); 
  _writeRegisterMultiBits(WM8960_REG_PLL_K_2,8,0,two); 
  _writeRegisterMultiBits(WM8960_REG_PLL_K_3,8,0,three); 
}

// 0=integer, 1=fractional
void setSMD(uint8_t mode)
{
  _writeRegisterBit(WM8960_REG_PLL_N, 5, mode);
}

 // 0=MCLK, 1=PLL_output
void setCLKSEL(uint8_t sel)
{
  _writeRegisterBit(WM8960_REG_CLOCKING_1, 0, sel);
}

// (0=divide by 1), (2=div by 2) *1 and 3 are "reserved"
void setSYSCLKDIV(uint8_t div) 
{
  _writeRegisterMultiBits(WM8960_REG_CLOCKING_1,2,1,div);  
}

// 000 = SYSCLK / (1.0*256). See ds pg 57 for other options
void setADCDIV(uint8_t div) 
{
  _writeRegisterMultiBits(WM8960_REG_CLOCKING_1,8,6,div);  
}

// 000 = SYSCLK / (1.0*256). See ds pg 57 for other options
void setDACDIV(uint8_t div) 
{
  _writeRegisterMultiBits(WM8960_REG_CLOCKING_1,5,3,div);  
}

void setBCLKDIV(uint8_t div)
{
  _writeRegisterMultiBits(WM8960_REG_CLOCKING_2,3,0,div);  
}

// Class D amp, 111= SYSCLK/16, so 11.2896MHz/16 = 705.6KHz
void setDCLKDIV(uint8_t div) 
{
  _writeRegisterMultiBits(WM8960_REG_CLOCKING_2,8,6,div);
}

void setALRCGPIO()
{
  // This setting should not be changed if ADCs are enabled.
  _writeRegisterBit(WM8960_REG_AUDIO_INTERFACE_2, 6, 1);
}

void enableMasterMode()
{
  _writeRegisterBit(WM8960_REG_AUDIO_INTERFACE_1, 6, 1);
}

void enablePeripheralMode()
{
  _writeRegisterBit(WM8960_REG_AUDIO_INTERFACE_1, 6, 0);
}

void setWL(uint8_t word_length)
{
  _writeRegisterMultiBits(WM8960_REG_AUDIO_INTERFACE_1,3,2,word_length);  
}

void setLRP(uint8_t polarity)
{
  _writeRegisterBit(WM8960_REG_AUDIO_INTERFACE_1, 4, polarity);
}

void setALRSWAP(uint8_t swap)
{
  _writeRegisterBit(WM8960_REG_AUDIO_INTERFACE_1, 8, swap);
}

void setVROI(uint8_t setting)
{
  _writeRegisterBit(WM8960_REG_ADDITIONAL_CONTROL_3, 6, setting);
}

void setVSEL(uint8_t setting)
{
  _writeRegisterMultiBits(WM8960_REG_ADDITIONAL_CONTROL_1,7,6,setting); 
}

// convertDBtoSetting
// This function will take in a dB value (as a float), and return the 
// corresponding volume setting necessary.
// For example, Headphone volume control goes from 47-120.
// While PGA gain control is from 0-63.
// The offset values allow for proper conversion.
//
// dB - float value of dB
//
// offset - the differnce from lowest dB value to lowest setting value
//
// stepSize - the dB step for each setting (aka the "resolution" of the setting)
// This is 0.75dB for the PGAs, 0.5 for ADC/DAC, and 1dB for most other amps.
//
// minDB - float of minimum dB setting allowed, note this is not mute on the 
// amp. "True mute" is always one stepSize lower.
//
// maxDB - float of maximum dB setting allowed. If you send anything higher, it
// will be limited to this max value.
uint8_t convertDBtoSetting(float dB, float offset, float stepSize, float minDB, float maxDB)
{
  // Limit incoming dB values to acceptable range. Note, the minimum limit we
  // want to limit this too is actually one step lower than the minDB, because
  // that is still an acceptable dB level (it is actually "true mute").
  // Note, the PGA amp does not have a "true mute" setting available, so we 
  // must check for its unique minDB of -17.25.

  // Limit max. This is the same for all amps.
  if (dB > maxDB) dB = maxDB;

  // PGA amp doesn't have mute setting, so minDB should be limited to minDB
  // Let's check for the PGAs unique minDB (-17.25) to know we are currently
  // converting a PGA setting.
  if(minDB == WM8960_PGA_GAIN_MIN) 
  {
    if (dB < minDB) dB = minDB;
  }
  else // Not PGA. All other amps have a mute setting below minDb
  {
    if (dB < (minDB - stepSize)) dB = (minDB - stepSize);
  }

  // Adjust for offset
  // Offset is the number that gets us from the minimum dB option of an amp
  // up to the minimum setting value in the register.
  dB = dB + offset; 

  // Find out how many steps we are above the minimum (at this point, our 
  // minimum is "0". Note, because dB comes in as a float, the result of this 
  // division (volume) can be a partial number. We will round that next.
  float volume = dB / stepSize;

  volume = round(volume); // round to the nearest setting value.

  // Serial debug (optional)
  // Serial.print("\t");
  // Serial.print((uint8_t)volume);

  return (uint8_t)volume; // cast from float to unsigned 8-bit integer.
}
